jjwuuu/PicoScanner-Station-Server/Code/Pico W/rickroll_gpio14_test.py

"""GPIO 14 Pico W piezo test.

This is a MicroPython port of the Arduino melody source supplied with this project.
Wire a passive piezo's positive lead to GP14 and its negative lead to GND.
Save as main.py on the Pico W to run it once after boot.
"""

from machine import PWM, Pin
import time


BUZZER_PIN = 14
TEMPO = 114
VOLUME = 32768  # 50% duty makes the strongest piezo square wave

# Frequency/divider pairs. Negative dividers are dotted notes.
MELODY = (
    587, -4, 659, -4, 440, 4, 659, -4, 740, -4, 880, 16, 784, 16, 740, 8,
    587, -4, 659, -4, 440, 2, 440, 16, 440, 16, 494, 16, 587, 8, 587, 16,
    587, -4, 659, -4, 440, 4, 659, -4, 740, -4, 880, 16, 784, 16, 740, 8,
    587, -4, 659, -4, 440, 2, 440, 16, 440, 16, 494, 16, 587, 8, 587, 16,
    0, 4, 494, 8, 554, 8, 587, 8, 587, 8, 659, 8, 554, -8, 494, 16,
    440, 2, 0, 4, 0, 8, 494, 8, 494, 8, 554, 8, 587, 8, 494, 4,
    440, 8, 880, 8, 0, 8, 880, 8, 659, -4, 0, 4, 494, 8, 494, 8,
    554, 8, 587, 8, 494, 8, 587, 8, 659, 8, 0, 8, 0, 8, 554, 8,
    494, 8, 440, -4, 0, 4, 0, 8, 494, 8, 494, 8, 554, 8, 587, 8,
    494, 8, 440, 4, 659, 8, 659, 8, 659, 8, 740, 8, 659, 4, 0, 4,
    587, 2, 659, 8, 740, 8, 587, 8, 659, 8, 659, 8, 659, 8, 740, 8,
    659, 4, 440, 4, 0, 2, 494, 8, 554, 8, 587, 8, 494, 8, 0, 8,
    659, 8, 740, 8, 659, -4, 440, 16, 494, 16, 587, 16, 494, 16, 740, -8,
    740, -8, 659, -4, 440, 16, 494, 16, 587, 16, 494, 16, 659, -8, 659, -8,
    587, -8, 554, 16, 494, -8, 440, 16, 494, 16, 587, 16, 494, 16, 587, 4,
    659, 8, 554, -8, 494, 16, 440, 8, 440, 8, 440, 8, 659, 4, 587, 2,
    440, 16, 494, 16, 587, 16, 494, 16, 740, -8, 740, -8, 659, -4, 440, 16,
    494, 16, 587, 16, 494, 16, 880, 4, 554, 8, 587, -8, 554, 16, 494, 8,
    440, 16, 494, 16, 587, 16, 494, 16, 587, 4, 659, 8, 554, -8, 494, 16,
    440, 4, 440, 8, 659, 4, 587, 2, 0, 4, 0, 8, 494, 8, 587, 8,
    494, 8, 587, 8, 659, 4, 0, 8, 0, 8, 554, 8, 494, 8, 440, -4,
    0, 4, 0, 8, 494, 8, 494, 8, 554, 8, 587, 8, 494, 8, 440, 4,
    0, 8, 880, 8, 880, 8, 659, 8, 740, 8, 659, 8, 587, 8, 0, 8,
    440, 8, 494, 8, 554, 8, 587, 8, 494, 8, 0, 8, 554, 8, 494, 8,
    440, -4, 0, 4, 494, 8, 494, 8, 554, 8, 587, 8, 494, 8, 440, 4,
    0, 8, 0, 8, 659, 8, 659, 8, 740, 4, 659, -4, 587, 2, 587, 8,
    659, 8, 740, 8, 659, 4, 659, 8, 659, 8, 740, 8, 659, 8, 440, 8,
    440, 4, 0, -4, 440, 8, 494, 8, 554, 8, 587, 8, 494, 8, 0, 8,
    659, 8, 740, 8, 659, -4, 440, 16, 494, 16, 587, 16, 494, 16, 740, -8,
    740, -8, 659, -4, 440, 16, 494, 16, 587, 16, 494, 16, 659, -8, 659, -8,
    587, -8, 554, 16, 494, 8, 440, 16, 494, 16, 587, 16, 494, 16, 587, 4,
    659, 8, 554, -8, 494, 16, 440, 4, 440, 8, 659, 4, 587, 2, 440, 16,
    494, 16, 587, 16, 494, 16, 740, -8, 740, -8, 659, -4, 440, 16, 494, 16,
    587, 16, 494, 16, 880, 4, 554, 8, 587, -8, 554, 16, 494, 8, 440, 16,
    494, 16, 587, 16, 494, 16, 587, 4, 659, 8, 554, -8, 494, 16, 440, 4,
    440, 8, 659, 4, 587, 2, 440, 16, 494, 16, 587, 16, 494, 16, 740, -8,
    740, -8, 659, -4, 440, 16, 494, 16, 587, 16, 494, 16, 880, 4, 554, 8,
    587, -8, 554, 16, 494, 8, 440, 16, 494, 16, 587, 16, 494, 16, 587, 4,
    659, 8, 554, -8, 494, 16, 440, 4, 440, 8, 659, 4, 587, 2, 440, 16,
    494, 16, 587, 16, 494, 16, 740, -8, 740, -8, 659, -4, 440, 16, 494, 16,
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
)


buzzer = PWM(Pin(BUZZER_PIN))
buzzer.duty_u16(0)


def duration_for(divider):
    whole_note_ms = (60000 * 4) // TEMPO
    duration_ms = whole_note_ms // abs(divider)
    return (duration_ms * 3) // 2 if divider < 0 else duration_ms


def play_note(frequency, duration_ms):
    sounding_ms = (duration_ms * 9) // 10
    if frequency:
        buzzer.freq(frequency)
        buzzer.duty_u16(VOLUME)
    time.sleep_ms(sounding_ms)
    buzzer.duty_u16(0)
    time.sleep_ms(duration_ms - sounding_ms)


def play_song():
    for index in range(0, len(MELODY), 2):
        play_note(MELODY[index], duration_for(MELODY[index + 1]))


try:
    print("Playing GPIO 14 piezo test")
    play_song()
    print("Finished")
finally:
    buzzer.duty_u16(0)
    buzzer.deinit() 
